charlie-x/LayerOne_2024/L1_POVSpinner/L12024POV/l1logostrip_test.h

#ifndef L1_STRIP_IMAGE_DATA_H
#define L1_STRIP_IMAGE_DATA_H

#include <stdint.h>

const uint16_t l1_strip_image_data[] PROGMEM = {
0b000001010101101010101010101010101010011111010101,

};

#endif // IMAGE_DATA_H
